xxxpokemon/pws/artwork/IMG_20151007_190225.jpg

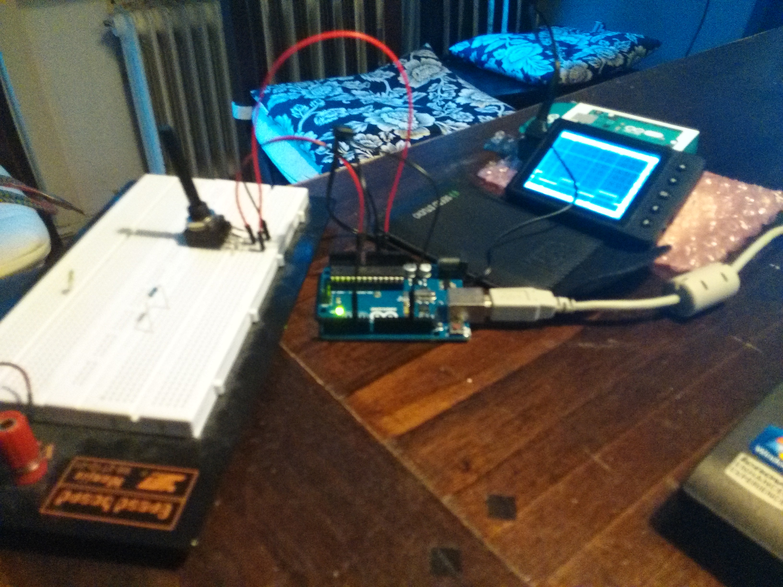
artwork/IMG_20151007_190225.jpg
